kasasiki3/HIDtaiko/docs/img/boot_button.jpg

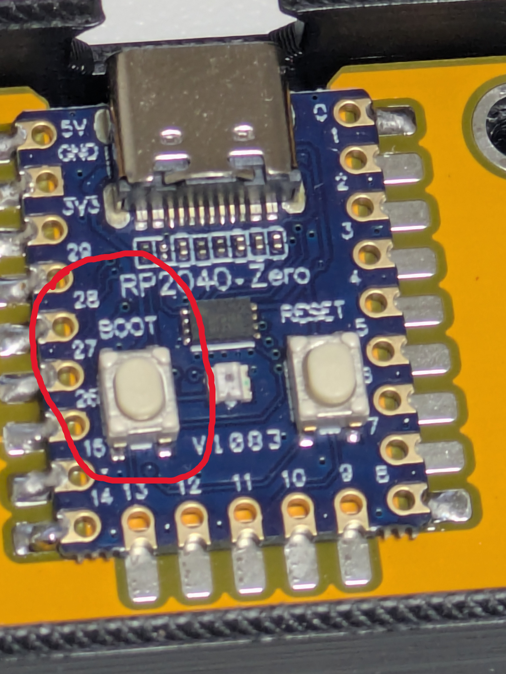
docs/img/boot_button.jpg
