kasasiki3/HIDtaiko/docs/img/DL.png

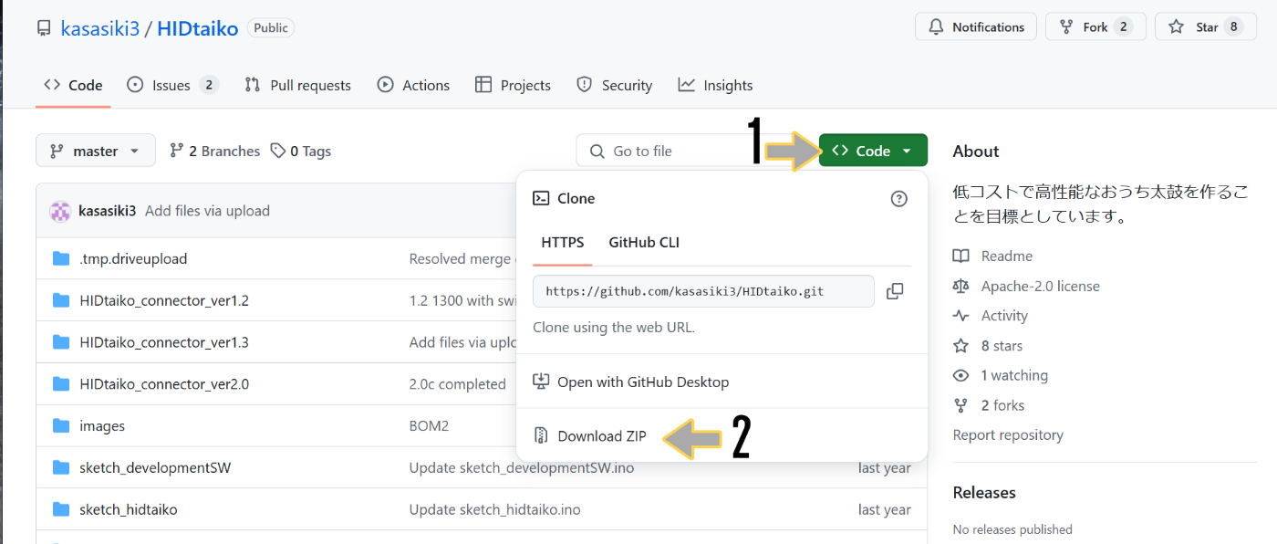
docs/img/DL.png
