kasasiki3/HIDtaiko/docs/img/fw_release.png

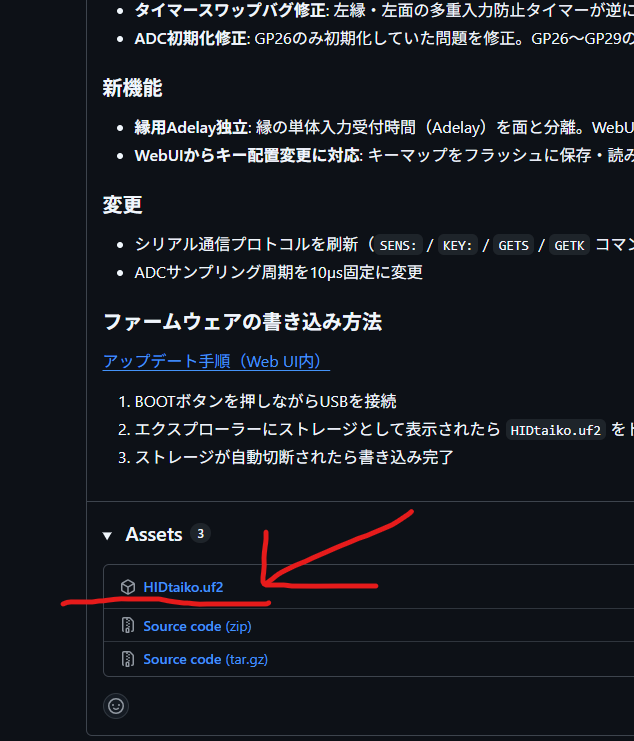
docs/img/fw_release.png
