kasasiki3/HIDtaiko/docs/img/スクリーンショット 2025-01-28 105332.png

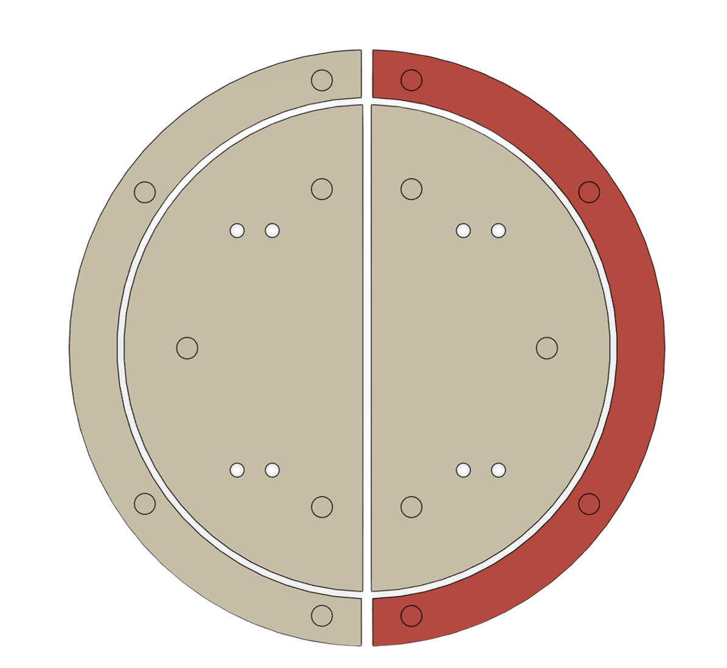
docs/img/スクリーンショット 2025-01-28 105332.png
