kasasiki3/HIDtaiko/docs/img/スクリーンショット 2026-08-26 122152.png

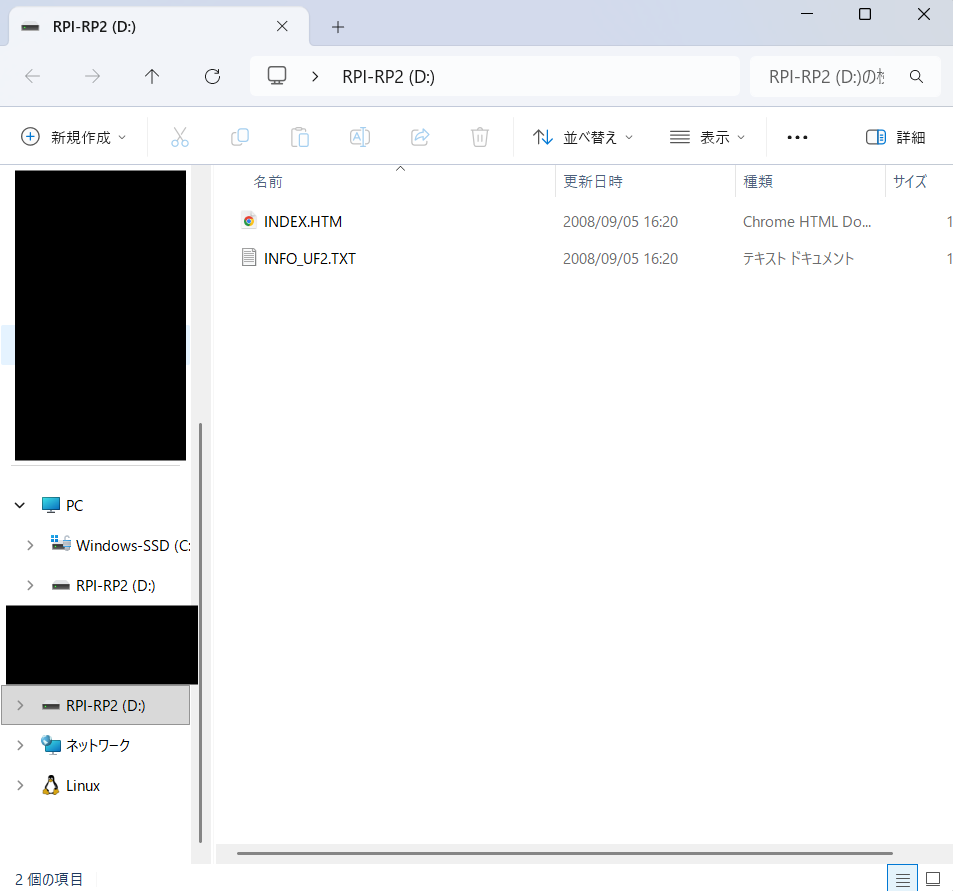
docs/img/スクリーンショット 2026-08-26 122152.png
