kasasiki3/HIDtaiko/drumhead/images/sensor position.png

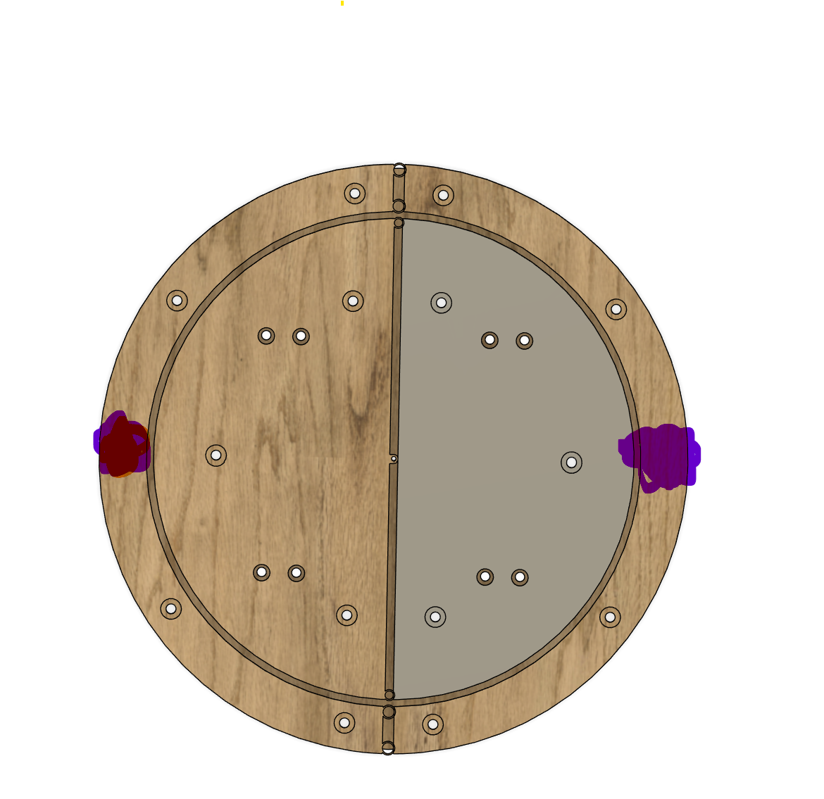
drumhead/images/sensor position.png
