kasasiki3/HIDtaiko/HIDtaiko_connector_ver2.0/image/image0.jpg

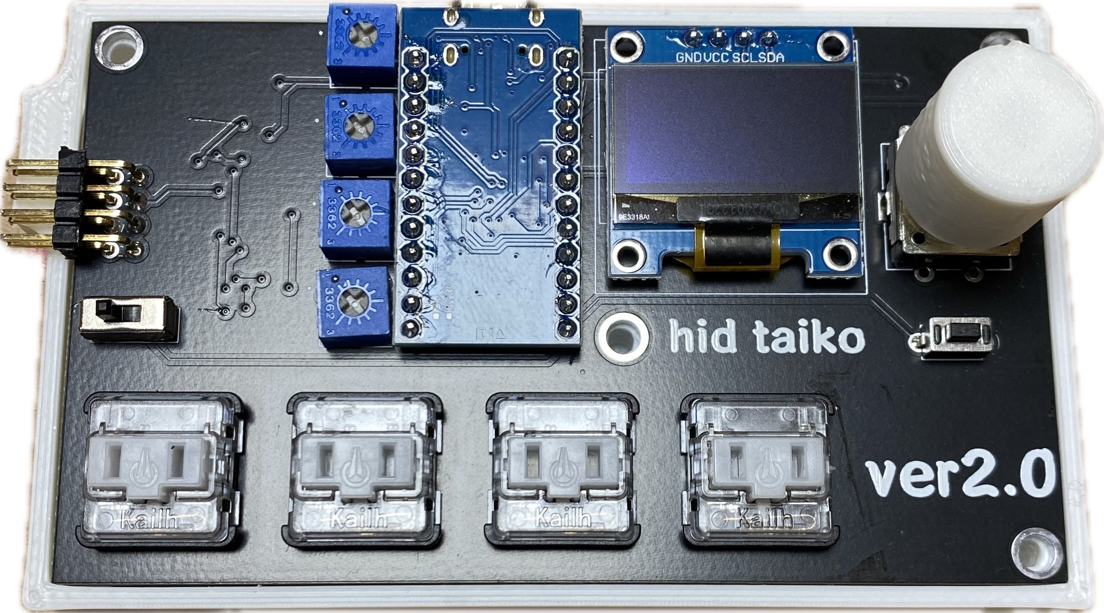
HIDtaiko_connector_ver2.0/image/image0.jpg
