kasasiki3/HIDtaiko/HIDtaiko_connector_rp2040/images/rp2040build guide/12.jpg

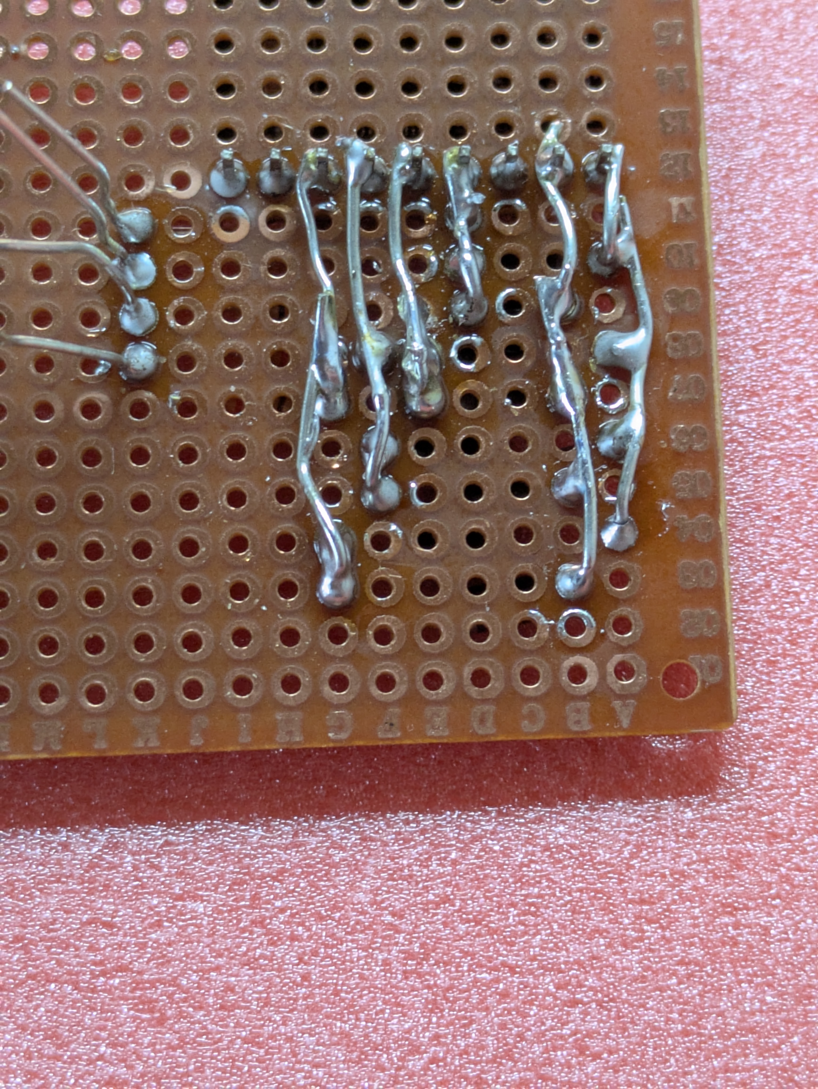
HIDtaiko_connector_rp2040/images/rp2040build guide/12.jpg
