kasasiki3/HIDtaiko/HIDtaiko_connector_rp2040/rp2_common/hardware_irq/irq.c

/*
 * Copyright (c) 2020 Raspberry Pi (Trading) Ltd.
 *
 * SPDX-License-Identifier: BSD-3-Clause
 */

#include "hardware/irq.h"
#include "pico/runtime_init.h"

#include "hardware/claim.h"
#include "pico/mutex.h"
#include "pico/assert.h"

#if defined(PICO_RUNTIME_INIT_PER_CORE_IRQ_PRIORITIES) && !PICO_RUNTIME_SKIP_INIT_PER_CORE_IRQ_PRIORITIES
PICO_RUNTIME_INIT_FUNC_PER_CORE(runtime_init_per_core_irq_priorities, PICO_RUNTIME_INIT_PER_CORE_IRQ_PRIORITIES);
#endif

#if PICO_VTABLE_PER_CORE
static uint8_t user_irq_claimed[NUM_CORES];
static inline uint8_t *user_irq_claimed_ptr(void) {
    return &user_irq_claimed[get_core_num()];
}
#else
static uint8_t user_irq_claimed;
static inline uint8_t *user_irq_claimed_ptr(void) {
    return &user_irq_claimed;
}
#endif

static inline irq_handler_t *get_vtable(void) {
#ifdef __riscv
    return (irq_handler_t *) (riscv_read_csr(RVCSR_MTVEC_OFFSET) & ~0x3u);
#else
    return (irq_handler_t *) scb_hw->vtor;
#endif
}

static inline void *add_thumb_bit(void *addr) {
#ifdef __riscv
    return addr;
#else
    return (void *) (((uintptr_t) addr) | 0x1);
#endif
}

static inline void *remove_thumb_bit(void *addr) {
#ifdef __riscv
    return addr;
#else
    return (void *) (((uintptr_t) addr) & (uint)~0x1);
#endif
}

static void set_raw_irq_handler_and_unlock(uint num, irq_handler_t handler, uint32_t save) {
    // update vtable (vtable_handler may be same or updated depending on cases, but we do it anyway for compactness)
    get_vtable()[VTABLE_FIRST_IRQ + num] = handler;
    __dmb();
    spin_unlock(spin_lock_instance(PICO_SPINLOCK_ID_IRQ), save);
}

void irq_set_enabled(uint num, bool enabled) {
    check_irq_param(num);
    // really should update irq_set_mask_enabled?
    irq_set_mask_n_enabled(num / 32, 1u << (num % 32), enabled);
}

bool irq_is_enabled(uint num) {
    check_irq_param(num);
#if PICO_RP2040
    return 0 != ((1u << num) & *((io_rw_32 *) (PPB_BASE + M0PLUS_NVIC_ISER_OFFSET)));
#elif defined(__riscv)
    return 0 != (hazard3_irqarray_read(RVCSR_MEIEA_OFFSET, num / 16) & (1u << (num % 16)));
#else
    return 0 != (nvic_hw->iser[num/32] & (1 << num % 32));
#endif
}

static inline void irq_set_mask_n_enabled_internal(uint n, uint32_t mask, bool enabled) {
    invalid_params_if(HARDWARE_IRQ, n * 32u >= ((NUM_IRQS + 31u) & ~31u));
#if defined(__riscv)
    if (enabled) {
        hazard3_irqarray_clear(RVCSR_MEIFA_OFFSET, 2 * n, mask & 0xffffu);
        hazard3_irqarray_clear(RVCSR_MEIFA_OFFSET, 2 * n + 1, mask >> 16);
        hazard3_irqarray_set(RVCSR_MEIEA_OFFSET, 2 * n, mask & 0xffffu);
        hazard3_irqarray_set(RVCSR_MEIEA_OFFSET, 2 * n + 1, mask >> 16);
    } else {
        hazard3_irqarray_clear(RVCSR_MEIEA_OFFSET, 2 * n, mask & 0xffffu);
        hazard3_irqarray_clear(RVCSR_MEIEA_OFFSET, 2 * n + 1, mask >> 16);
    }
#elif PICO_RP2040
    ((void)n);
    if (enabled) {
        nvic_hw->icpr = mask;
        nvic_hw->iser = mask;
    } else {
        nvic_hw->icer = mask;
    }
#else
    // >32 IRQs (well this works for the bottom 32 which is all that is passed in
    if (enabled) {
        nvic_hw->icpr[n] = mask;
        nvic_hw->iser[n] = mask;
    } else {
        nvic_hw->icer[n] = mask;
    }
#endif
}

void irq_set_mask_enabled(uint32_t mask, bool enabled) {
    irq_set_mask_n_enabled_internal(0, mask, enabled);
}

void irq_set_mask_n_enabled(uint n, uint32_t mask, bool enabled) {
    irq_set_mask_n_enabled_internal(n, mask, enabled);
}

void irq_set_pending(uint num) {
    check_irq_param(num);
#ifdef __riscv
    // Interrupt force is subsequently cleared by any read of meinext that
    // indicates the forced IRQ (can also be cleared manually)
    hazard3_irqarray_set(RVCSR_MEIFA_OFFSET, num / 16, 1u << (num % 16));
#else
#if PICO_RP2040
    *((io_rw_32 *) (PPB_BASE + M0PLUS_NVIC_ISPR_OFFSET)) = 1u << num;
#else
    nvic_hw->ispr[num/32] = 1 << (num % 32);
#endif
#endif
}

#if !PICO_DISABLE_SHARED_IRQ_HANDLERS
// limited by 8 bit relative links (and reality)
static_assert(PICO_MAX_SHARED_IRQ_HANDLERS >= 1 && PICO_MAX_SHARED_IRQ_HANDLERS < 0x7f, "");

// note these are not real functions, they are code fragments (i.e. don't call them)
extern void irq_handler_chain_first_slot(void);
extern void irq_handler_chain_remove_tail(void);

// On Arm:
//
// - The first slot begins with a tail call to irq_handler_chain_first_slot, passing a pointer to
//   the slot in r1; this pushes the initial link register to the stack, invokes the slot's handler
//   and then returns into the latter half of the slot
//
// - Non-first slots begin with a call of the slot's handler
//
// - Non-last slots end with a tail into the next slot in the chain
//
// - The last slot ends with a pop of the return address pushed by irq_handler_chain_first_slot
//
// On RISC-V:
//
// - The first slot begins with jal t0, irq_handler_first_chain_slot followed by a 32-bit pointer to
//   the handler; this pushes the ultimate return address to the stack, invokes the slot's handler
//   and then returns into the latter half of the slot
//
// - Non-first slots begin with an lui; jalr sequence to call the handler
//
// - Non-last slots end with a tail into the next slot in the chain
//
// - The last slot ends with a pop of the return address pushed by irq_handler_chain_first_slot
//
// This means the layout is different between Arm and RISC-V (though total size is the same): Arm is
// 6 bytes of code, 2 bytes of link and 4 bytes of pointer. RISC-V is 10 bytes of code and 2 bytes
// of link.

extern struct irq_handler_chain_slot {
#ifndef __riscv
    uint16_t inst1;
    uint16_t inst2;
#else
    uint32_t inst1;
    uint32_t inst2;
#endif
    uint16_t inst3;
    union {
        // On Arm, when a handler is removed while executing, it needs a 32-bit instruction at
        // inst3, which overwrites the link and the priority; this is ok because no one else is
        // modifying the chain, as the chain is effectively core-local, and the user code which
        // might still need this link disables the IRQ in question before updating, which means we
        // aren't executing!
        struct {
            int8_t link;
            uint8_t priority;
        };
        uint16_t inst4;
    };
#ifndef __riscv
    irq_handler_t handler;
#endif
} irq_handler_chain_slots[PICO_MAX_SHARED_IRQ_HANDLERS];

static int8_t irq_handler_chain_free_slot_head;

static inline bool is_shared_irq_raw_handler(irq_handler_t raw_handler) {
    return (uintptr_t)raw_handler - (uintptr_t)irq_handler_chain_slots < sizeof(irq_handler_chain_slots);
}

bool irq_has_shared_handler(uint irq_num) {
    check_irq_param(irq_num);
    irq_handler_t handler = irq_get_vtable_handler(irq_num);
    return handler && is_shared_irq_raw_handler(handler);
}

#else // PICO_DISABLE_SHARED_IRQ_HANDLERS
#define is_shared_irq_raw_handler(h) false
bool irq_has_shared_handler(uint irq_num) {
    return false;
}
#endif


irq_handler_t irq_get_vtable_handler(uint num) {
    check_irq_param(num);
    return get_vtable()[VTABLE_FIRST_IRQ + num];
}

void irq_set_exclusive_handler(uint num, irq_handler_t handler) {
    check_irq_param(num);
#if !PICO_NO_RAM_VECTOR_TABLE
    spin_lock_t *lock = spin_lock_instance(PICO_SPINLOCK_ID_IRQ);
    uint32_t save = spin_lock_blocking(lock);
    __unused irq_handler_t current = irq_get_vtable_handler(num);
    hard_assert(current == __unhandled_user_irq || current == handler);
    set_raw_irq_handler_and_unlock(num, handler, save);
#else
    panic_unsupported();
#endif
}

irq_handler_t irq_get_exclusive_handler(uint num) {
    check_irq_param(num);
#if !PICO_NO_RAM_VECTOR_TABLE
    spin_lock_t *lock = spin_lock_instance(PICO_SPINLOCK_ID_IRQ);
    uint32_t save = spin_lock_blocking(lock);
    irq_handler_t current = irq_get_vtable_handler(num);
    spin_unlock(lock, save);
    if (current == __unhandled_user_irq || is_shared_irq_raw_handler(current)) {
        return NULL;
    }
    return current;
#else
    panic_unsupported();
#endif
}


#if !PICO_DISABLE_SHARED_IRQ_HANDLERS

#ifndef __riscv

static uint16_t make_j_16(uint16_t *from, void *to) {
    uint32_t ui_from = (uint32_t)from;
    uint32_t ui_to = (uint32_t)to;
    int32_t delta = (int32_t)(ui_to - ui_from - 4);
    assert(delta >= -2048 && delta <= 2046 && !(delta & 1));
    return (uint16_t)(0xe000 | ((delta >> 1) & 0x7ff));
}

static void insert_bl_32(uint16_t *from, void *to) {
    uint32_t ui_from = (uint32_t)from;
    uint32_t ui_to = (uint32_t)to;
    uint32_t delta = (ui_to - ui_from - 4) / 2;
    assert(!(delta >> 11u));
    from[0] = (uint16_t)(0xf000 | ((delta >> 11u) & 0x7ffu));
    from[1] = (uint16_t)(0xf800 | (delta & 0x7ffu));
}

static inline void *resolve_j_16(uint16_t *inst) {
    assert(0x1c == (*inst)>>11u);
    int32_t i_addr = (*inst) << 21u;
    i_addr /= (int32_t)(1u<<21u);
    return inst + 2 + i_addr;
}

#else

static uint16_t make_jal_16(uint16_t *from, void *to) {
    uint32_t ui_from = (uint32_t)from;
    uint32_t ui_to = (uint32_t)to;
    int32_t delta = (int32_t)(ui_to - ui_from);
    assert(delta >= -2048 && delta <= 2046 && !(delta & 1));
    return 0x2001u | riscv_encode_imm_cj((uint32_t)delta);
}

static uint16_t make_j_16(uint16_t *from, void *to) {
    return 0x8000u | make_jal_16(from, to);
}

static inline uint32_t make_call_inst1(void *to) {
    // lui ra, %hi(to)
    return 0x000000b7u | riscv_encode_imm_u_hi((uintptr_t)to);
}
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
